ZeroZeroOne-dev/00Key/images/3.jpeg

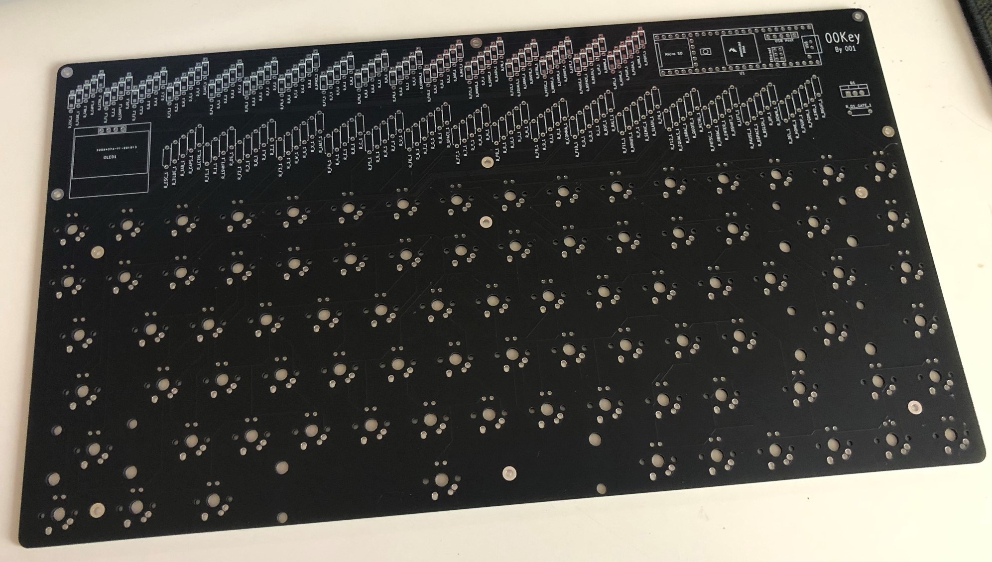
images/3.jpeg
