ZeroZeroOne-dev/00Key/firmware/src/OLED.cpp

#include <Arduino.h>
#include <Adafruit_GFX.h>
#include <Adafruit_SSD1306.h>
#include <Fonts/FreeSans9pt7b.h>
#include <Fonts/FreeSansBold9pt7b.h>
#include "OLED.h"

Adafruit_SSD1306 display(128, 64, &Wire2, -1);

bool _capsOn = false;
int _layer = 0;
int _blPercentage = 0;
char _rValue[3];
char _gValue[3];
char _bValue[3];

bool _splashScreenFinished = false;
int _splashScreenDuration = 3000;

// clang-format off

const unsigned char _logo[] PROGMEM = {
    0x00, 0x00, 0x00, 0x00, 0x00, 0x00, 0x00, 0x00, 0x00, 0x00, 0x00, 0x00, 0x00, 0x00, 0x00, 0x00, 
	0x00, 0x00, 0x00, 0x00, 0x00, 0x00, 0x00, 0x1f, 0xf8, 0x00, 0x00, 0x00, 0x00, 0x00, 0x00, 0x00, 
	0x00, 0x00, 0x00, 0x00, 0x00, 0x00, 0x01, 0xff, 0xff, 0x80, 0x00, 0x00, 0x00, 0x00, 0x00, 0x00, 
	0x00, 0x00, 0x00, 0x00, 0x00, 0x00, 0x0f, 0xff, 0xff, 0xf0, 0x00, 0x00, 0x00, 0x00, 0x00, 0x00, 
	0x00, 0x00, 0x80, 0x00, 0x00, 0x00, 0x3f, 0xff, 0xff, 0xfc, 0x00, 0x40, 0x00, 0x00, 0x80, 0x00, 
	0x00, 0x00, 0x00, 0x00, 0x00, 0x00, 0xff, 0xff, 0xff, 0xff, 0x00, 0x00, 0x00, 0x00, 0x00, 0x00, 
	0x00, 0x00, 0x00, 0x00, 0x00, 0x01, 0xff, 0xff, 0xff, 0xff, 0x80, 0x00, 0x00, 0x00, 0x00, 0x00, 
	0x00, 0x00, 0x00, 0x20, 0x00, 0x07, 0xff, 0xff, 0xff, 0xff, 0xe0, 0x00, 0x00, 0x00, 0x00, 0x00, 
	0x06, 0x00, 0x00, 0x00, 0x00, 0x0f, 0xff, 0xff, 0xff, 0xff, 0xf0, 0x00, 0x00, 0x00, 0x00, 0x60, 
	0x03, 0xe0, 0x00, 0x00, 0x00, 0x1f, 0xff, 0xff, 0xff, 0xff, 0xf8, 0x00, 0x00, 0x00, 0x07, 0xc0, 
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

	display.display();
}

void clearSplashScreen()
{
	_splashScreenFinished = true;
	draw();
}

void drawSplashScreen()
{
	display.drawBitmap(0, 0, _logo, 128, 64, WHITE); // display.drawBitmap(x position, y position, bitmap data, bitmap width, bitmap height, color)
	display.display();
}

void OLED::setup()
{
	display.begin(SSD1306_SWITCHCAPVCC, 0x3C);
	display.clearDisplay();
	display.setTextSize(1);

	display.setTextColor(WHITE);
	display.setTextWrap(false);
	setLayer(0);

	drawSplashScreen();
}

void OLED::loop()
{
	if (!_splashScreenFinished && millis() > _splashScreenDuration)
	{
		clearSplashScreen();
	}
}

void OLED::setLayer(int layer)
{
	_layer = layer;
	draw();
}

void OLED::setBacklight(int percentage)
{
	_blPercentage = percentage;
	draw();
}

void OLED::toggleCaps()
{
	_capsOn = !_capsOn;
	draw();
}

void OLED::setUnderglow(char* red, char* green, char* blue)
{
	strncpy(_rValue, red, 3);
	strncpy(_gValue, green, 3);
	strncpy(_bValue, blue, 3);
	draw();
}
