ZeroZeroOne-dev/00Key/firmware/include/OLED.h

#ifndef OLED_h
#define OLED_h

class OLED
{
public:
    static void setup();
    static void loop();
    static void setLayer(int layer);
    static void setBacklight(int percentage);
    static void toggleCaps();
    static void setUnderglow(char* red, char* green, char* blue);
};

#endif
