ZeroZeroOne-dev/00Key/firmware/src/Backlight.cpp

#include <Arduino.h>
#include "Backlight.h"
#include "OLED.h"
#include "Storage.h"

const byte ledPin = 28;
const byte step = 25;
byte currentLevel = 125;
byte maxLevel = 125;

void writeCurrent()
{
    analogWrite(ledPin, currentLevel);

    int percentage = (double)currentLevel / maxLevel * 100;

    OLED::setBacklight(percentage);
    Storage::set(StorageLocations::BL, currentLevel);
}

void Backlight::setup()
{
    currentLevel = Storage::get(StorageLocations::BL);

    pinMode(ledPin, OUTPUT);
    writeCurrent();
}

void Backlight::up()
{
    if (currentLevel < maxLevel)
    {
        currentLevel += step;
    }

    writeCurrent();
}

void Backlight::down()
{
    if (currentLevel > 0)
    {
        currentLevel -= step;
    }

    writeCurrent();
}
